eigenpi/The-Funky-Weather-Station/images/photo2.jpg

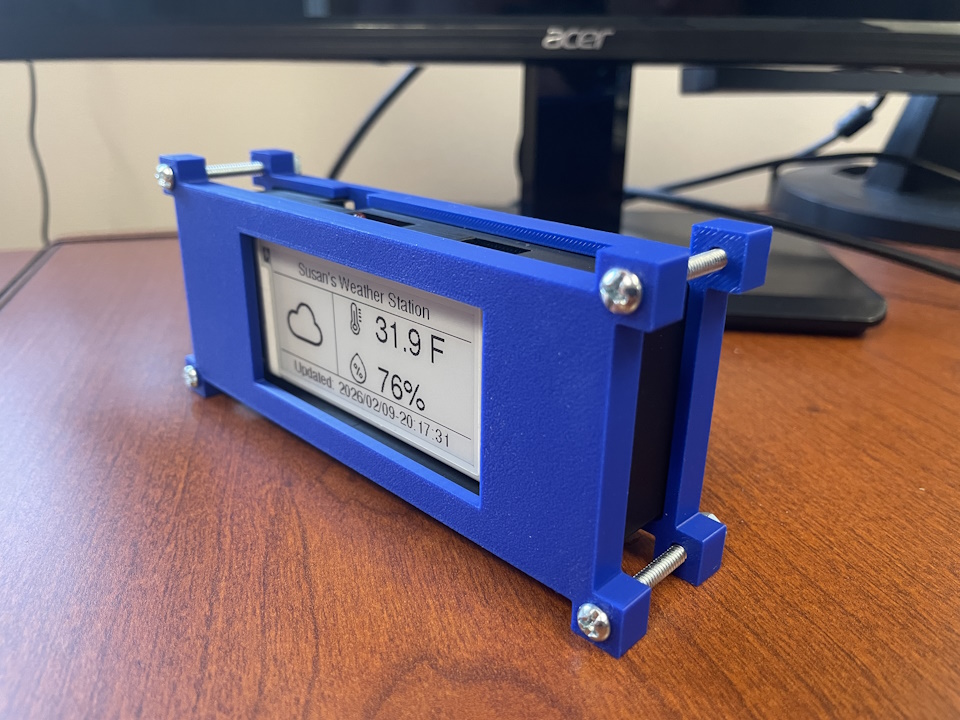
images/photo2.jpg
