eigenpi/The-Funky-Weather-Station/images/photo3.jpg

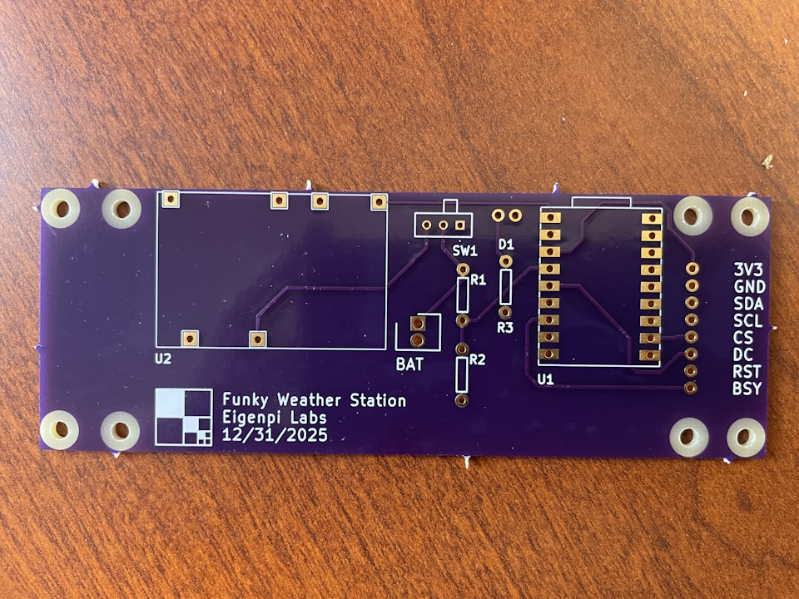
images/photo3.jpg
