eigenpi/The-Funky-Weather-Station/firmware_arduino_esp32c3/WeatherPaper_V1/icons.h

// icons used for showing weather forecast on e-paper display

const unsigned char epd_bitmap_broken_clouds [] PROGMEM = {
	0x00, 0x00, 0x00, 0x00, 0x00, 0x00, 0x00, 0x00, 0x00, 0x00, 0x00, 0x00, 0x00, 0x00, 0x00, 0x00, 
	0x00, 0x00, 0x00, 0x00, 0x00, 0x00, 0x00, 0x00, 0x00, 0x00, 0x00, 0x00, 0x00, 0x00, 0x00, 0x00, 
	0x00, 0x00, 0x00, 0x00, 0x00, 0x00, 0x00, 0x00, 0x00, 0x00, 0x00, 0x00, 0x00, 0x00, 0x00, 0x00, 
	0x00, 0x00, 0x00, 0x00, 0x00, 0x00, 0x00, 0x00, 0x00, 0x00, 0x00, 0x00, 0x00, 0x00, 0x00, 0x00, 
	0x00, 0x00, 0x00, 0x00, 0x00, 0x00, 0x00, 0x00, 0x00, 0x00, 0x00, 0x00, 0x00, 0x00, 0x00, 0x00, 
	0x00, 0x00, 0x00, 0x00, 0x00, 0x00, 0x00, 0x00, 0x00, 0x00, 0x00, 0x00, 0x00, 0x00, 0x00, 0x00, 
	0x00, 0x00, 0x00, 0x00, 0x00, 0x00, 0x00, 0x00, 0x00, 0x00, 0x00, 0x00, 0x3f, 0xc0, 0x00, 0x00, 
	0x00, 0x00, 0x00, 0x01, 0xff, 0xf8, 0x00, 0x00, 0x00, 0x00, 0x00, 0x07, 0xff, 0xfc, 0x00, 0x00, 
	0x00, 0x00, 0x00, 0x0f, 0xff, 0xff, 0x00, 0x00, 0x00, 0x00, 0x00, 0x1f, 0xc0, 0x3f, 0x80, 0x00, 
	0x00, 0x00, 0x00, 0x3f, 0x00, 0x0f, 0xc0, 0x00, 0x00, 0x00, 0x00, 0x7c, 0x00, 0x03, 0xe0, 0x00, 
	0x00, 0x00, 0x00, 0xfc, 0x00, 0x01, 0xe0, 0x00, 0x00, 0x00, 0x0f, 0xff, 0x00, 0x01, 0xf0, 0x00, 
	0x00, 0x00, 0x3f, 0xff, 0xc0, 0x00, 0xff, 0x80, 0x00, 0x00, 0x7f, 0xff, 0xe0, 0x00, 0x7f, 0xe0, 
	0x00, 0x00, 0xfe, 0x07, 0xf0, 0x00, 0x7f, 0xf0, 0x00, 0x01, 0xf8, 0x01, 0xf8, 0x00, 0x3f, 0xf8, 
	0x00, 0x03, 0xe0, 0x00, 0x7c, 0x00, 0x00, 0x7c, 0x00, 0x07, 0xc0, 0x00, 0x3e, 0x00, 0x00, 0x3e, 
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
	0x01, 0xc0, 0x03, 0x80, 0x00, 0xf0, 0x0f, 0x00, 0x00, 0x3f, 0xfc, 0x00, 0x00, 0x0f, 0xf0, 0x00
};
const unsigned char epd_bitmap_temperature [] PROGMEM = {
	0x00, 0x0f, 0x00, 0x00, 0x00, 0x1f, 0xc0, 0x00, 0x00, 0x30, 0xc0, 0x00, 0x00, 0x30, 0x60, 0x00, 
	0x00, 0x60, 0x67, 0x80, 0x00, 0x60, 0x67, 0x80, 0x00, 0x60, 0x60, 0x00, 0x00, 0x60, 0x63, 0x00, 
	0x00, 0x66, 0x67, 0x80, 0x00, 0x66, 0x60, 0x00, 0x00, 0x66, 0x60, 0x00, 0x00, 0x66, 0x67, 0x80, 
	0x00, 0x66, 0x67, 0x80, 0x00, 0x66, 0x60, 0x00, 0x00, 0x66, 0x60, 0x00, 0x00, 0x66, 0x67, 0x80, 
	0x00, 0x66, 0x67, 0x80, 0x00, 0x66, 0x60, 0x00, 0x00, 0x66, 0x60, 0x00, 0x00, 0xe6, 0x70, 0x00, 
	0x00, 0xc6, 0x38, 0x00, 0x01, 0x8f, 0x18, 0x00, 0x01, 0x9f, 0x98, 0x00, 0x01, 0xb0, 0xcc, 0x00, 
	0x01, 0x30, 0xcc, 0x00, 0x01, 0xb8, 0xcc, 0x00, 0x01, 0x9f, 0x98, 0x00, 0x01, 0x8f, 0x18, 0x00, 
	0x00, 0xc0, 0x30, 0x00, 0x00, 0x70, 0x70, 0x00, 0x00, 0x3f, 0xe0, 0x00, 0x00, 0x1f, 0x80, 0x00
};
const unsigned char epd_bitmap_warning [] PROGMEM = {
	0x00, 0x00, 0x03, 0xc0, 0x02, 0x40, 0x06, 0x60, 0x04, 0x20, 0x0d, 0xb0, 0x19, 0x98, 0x11, 0x88, 
	0x31, 0x8c, 0x21, 0x84, 0x60, 0x06, 0x40, 0x02, 0xc0, 0x03, 0xc0, 0x03, 0x7f, 0xfe, 0x00, 0x00
};
